spironoo/miro-cases/Images/3 Miros.jpg

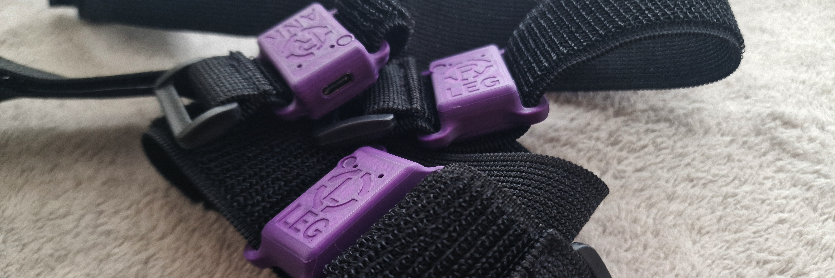
Images/3 Miros.jpg
