spironoo/miro-cases/Images/20251211_063059.jpg

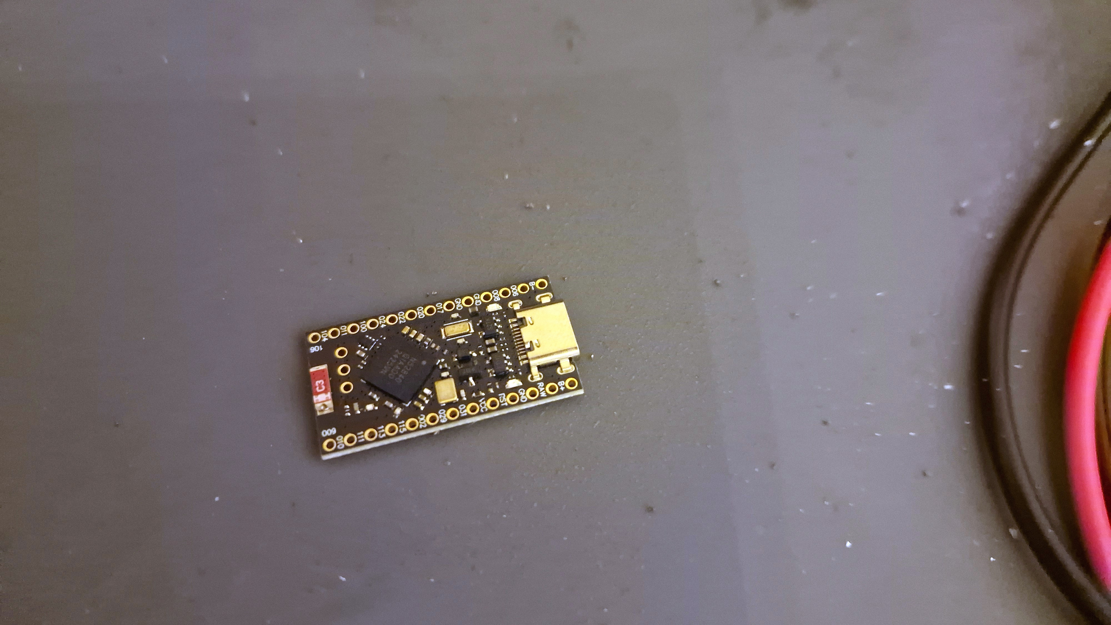
Images/20251211_063059.jpg
