spironoo/miro-cases/Images/20251211_063324.jpg

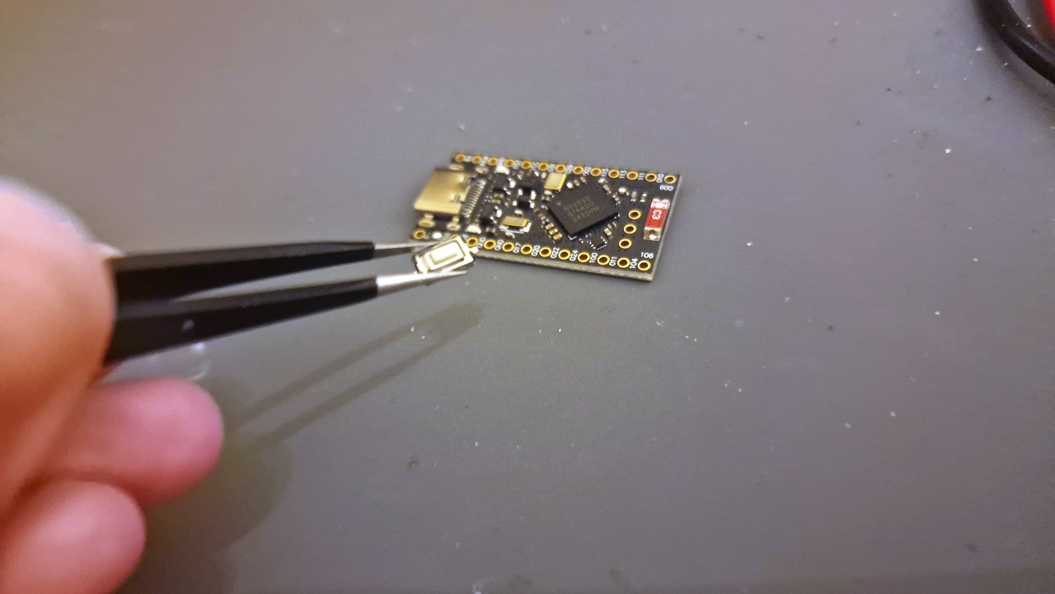
Images/20251211_063324.jpg
