spironoo/miro-cases/Images/20251211_063325.jpg

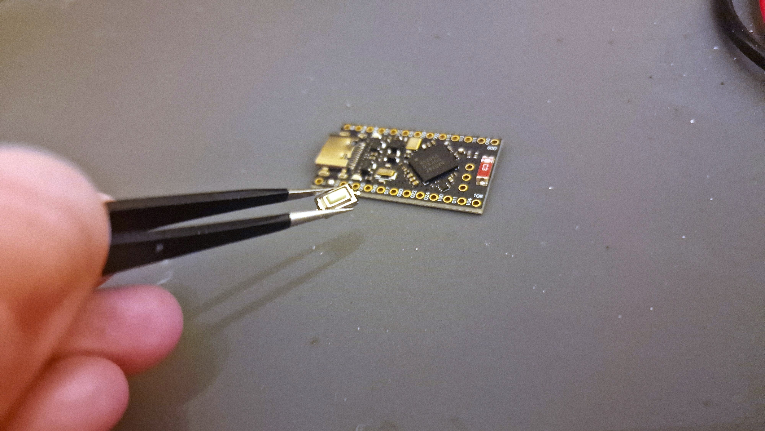
Images/20251211_063325.jpg
