spironoo/miro-cases/Images/20251211_063358.jpg

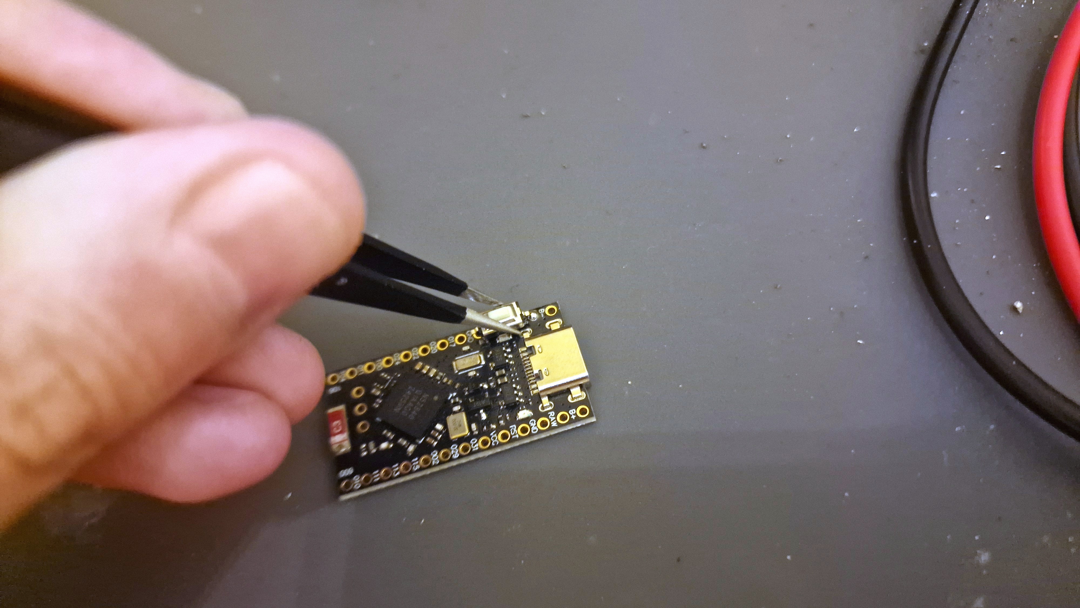
Images/20251211_063358.jpg
