spironoo/miro-cases/Images/20251211_063400.jpg

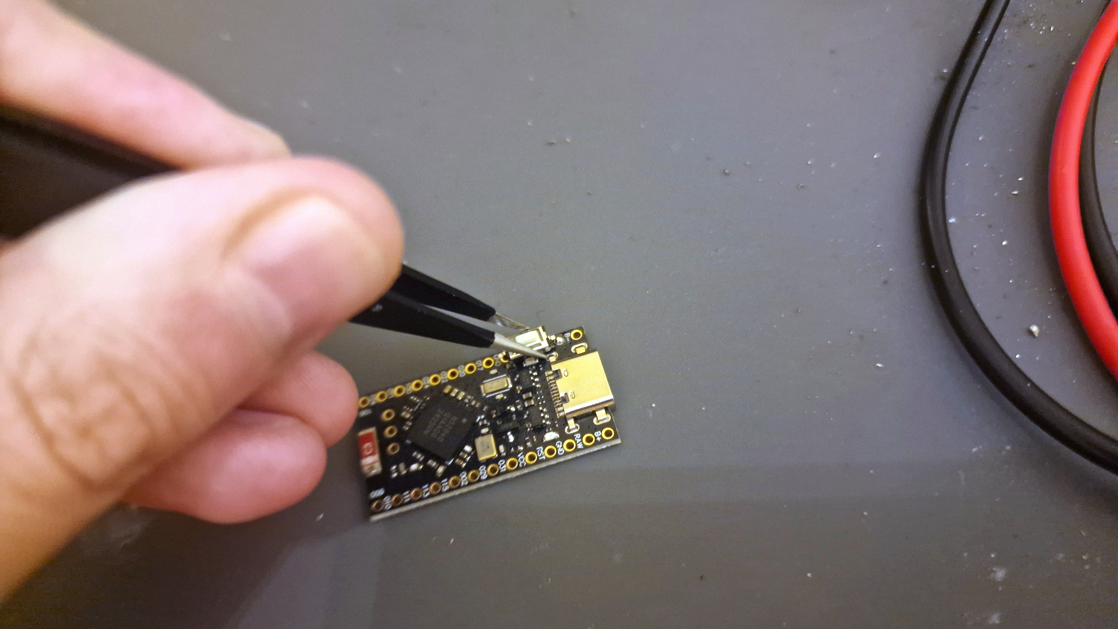
Images/20251211_063400.jpg
