spironoo/miro-cases/Images/20251211_063406.jpg

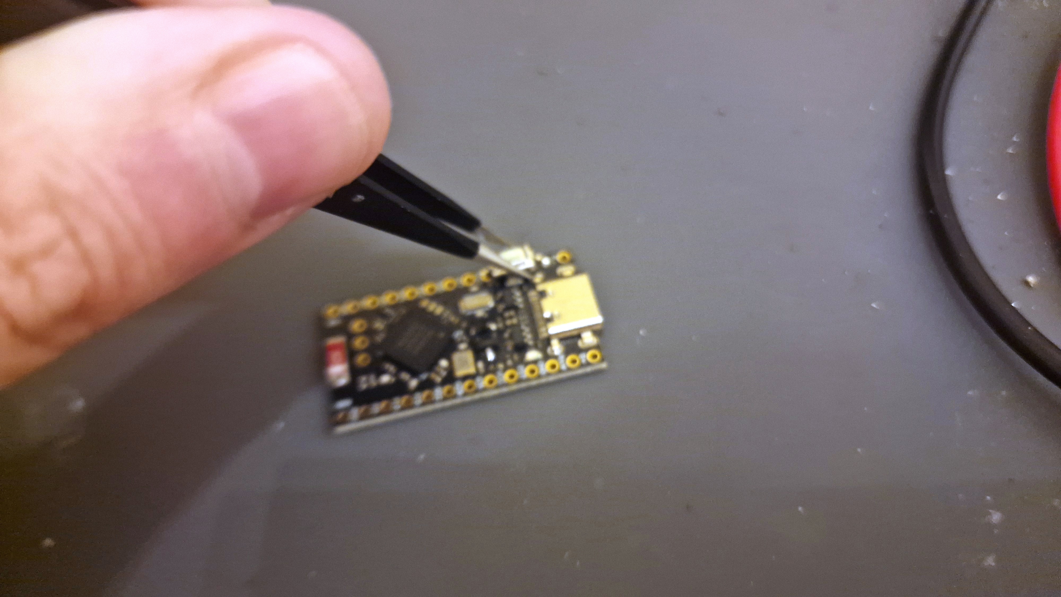
Images/20251211_063406.jpg
