spironoo/miro-cases/Images/20251211_063424.jpg

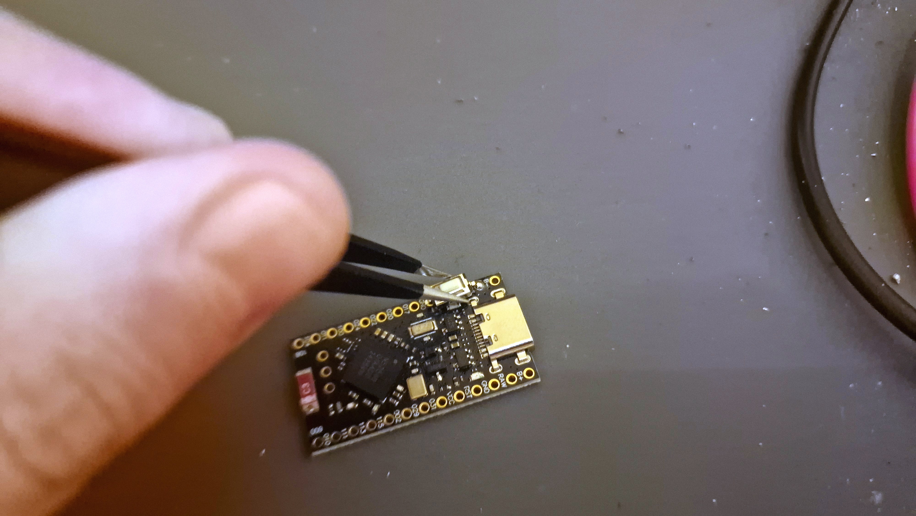
Images/20251211_063424.jpg
