spironoo/miro-cases/Images/20251211_063507.jpg

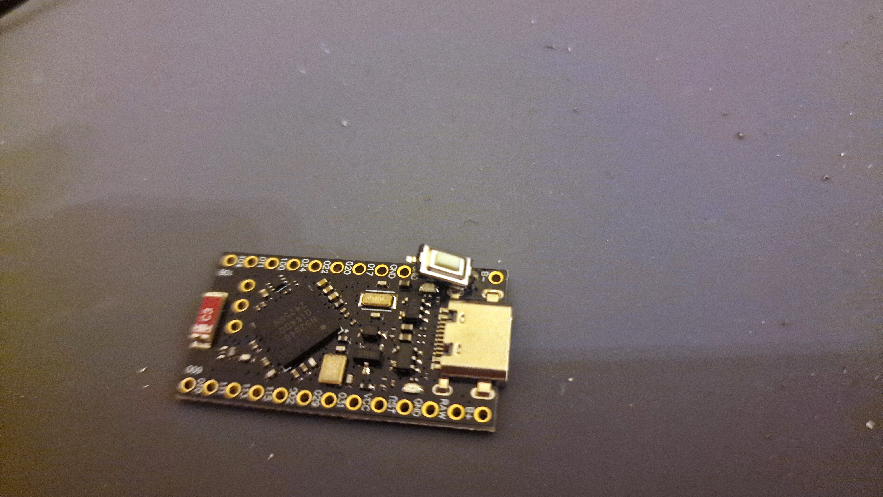
Images/20251211_063507.jpg
