spironoo/miro-cases/Images/20251211_063535.jpg

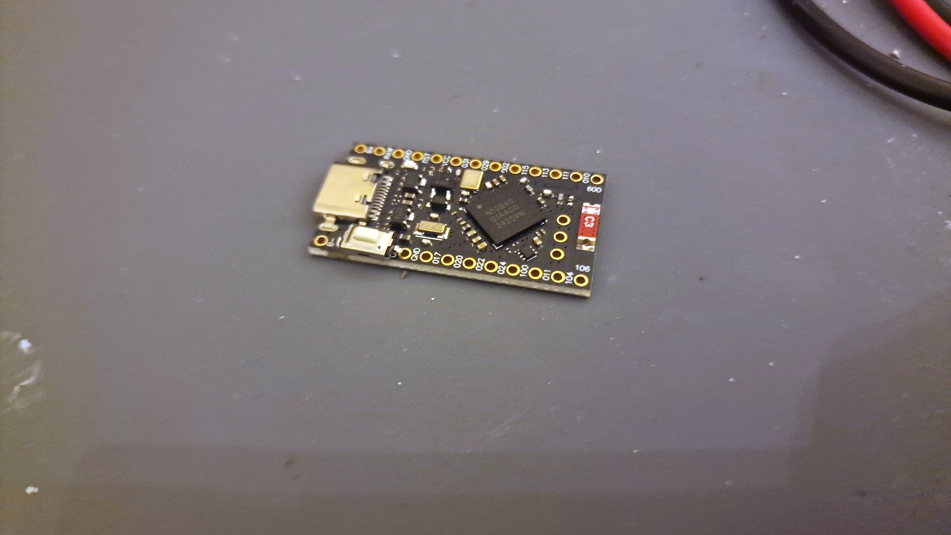
Images/20251211_063535.jpg
