spironoo/miro-cases/Images/20251211_063546.jpg

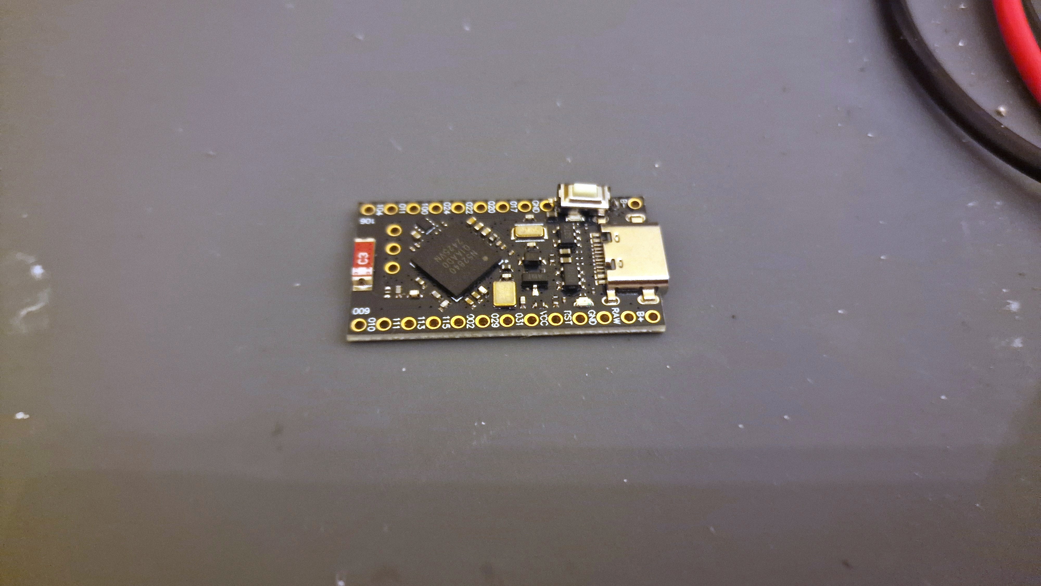
Images/20251211_063546.jpg
