spironoo/miro-cases/Images/20251211_063958.jpg

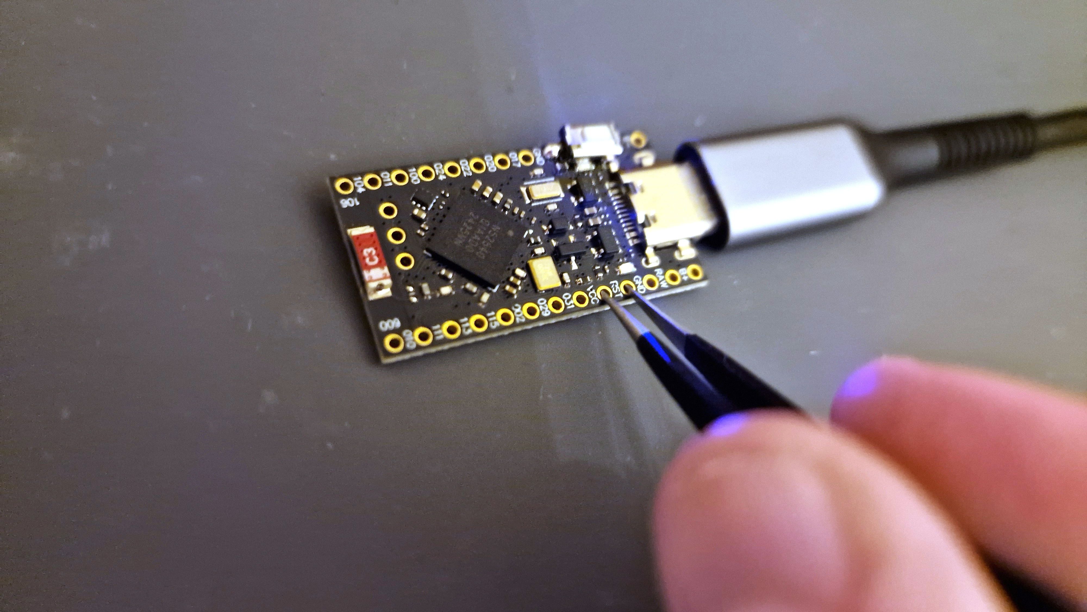
Images/20251211_063958.jpg
