spironoo/miro-cases/Images/20251211_064003.jpg

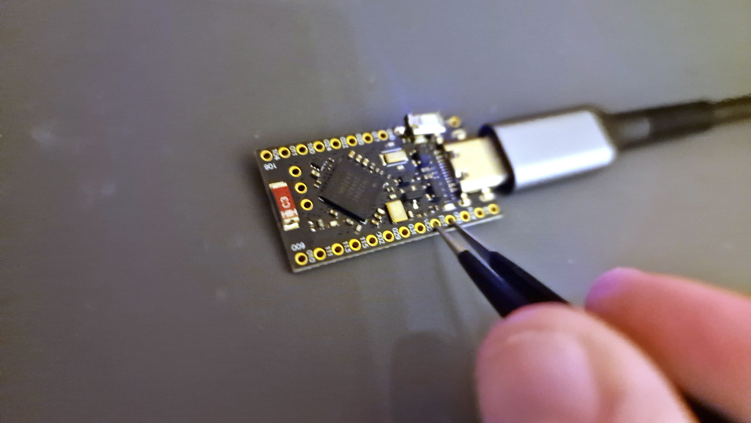
Images/20251211_064003.jpg
