spironoo/miro-cases/Images/20251211_064025.jpg

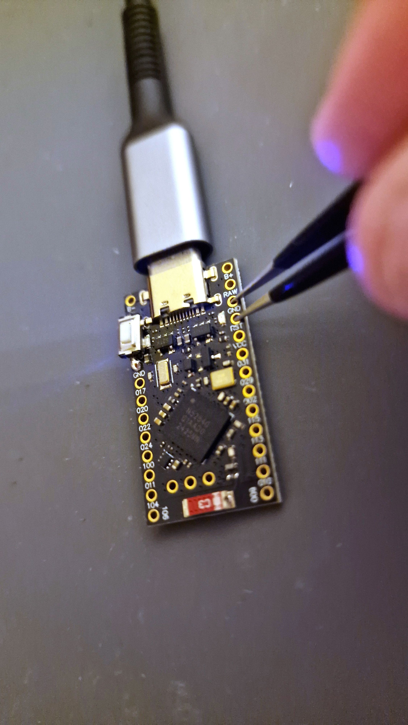
Images/20251211_064025.jpg
