spironoo/miro-cases/Images/20251211_065441.jpg

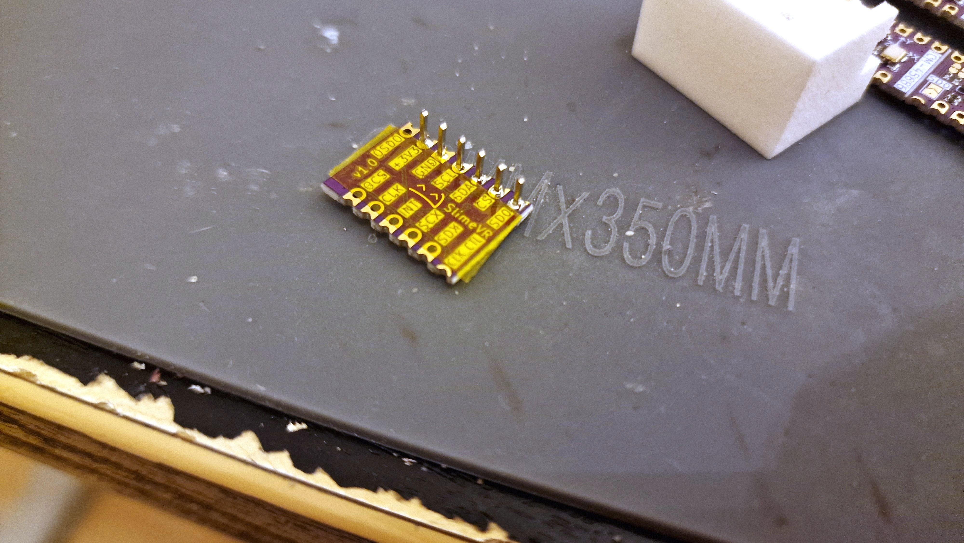
Images/20251211_065441.jpg
