spironoo/miro-cases/Images/20251211_070914.jpg

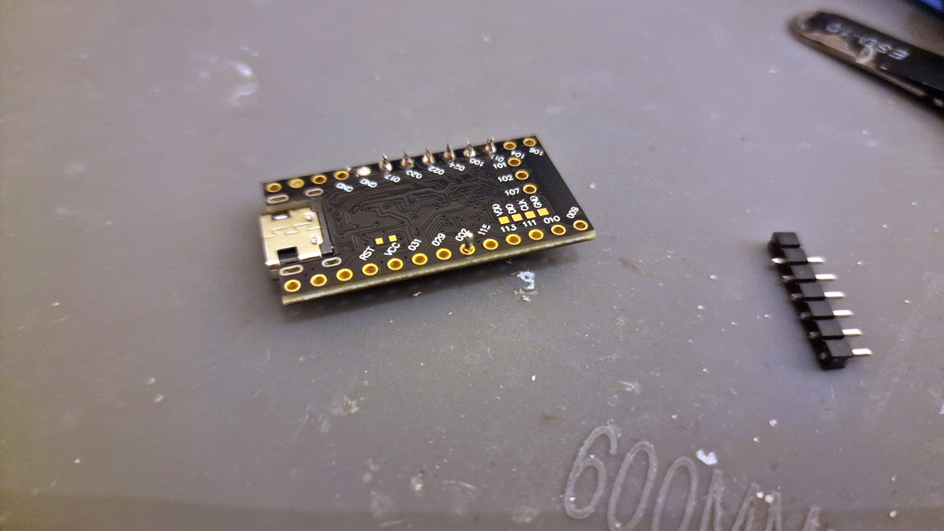
Images/20251211_070914.jpg
