spironoo/miro-cases/Images/20251211_070938.jpg

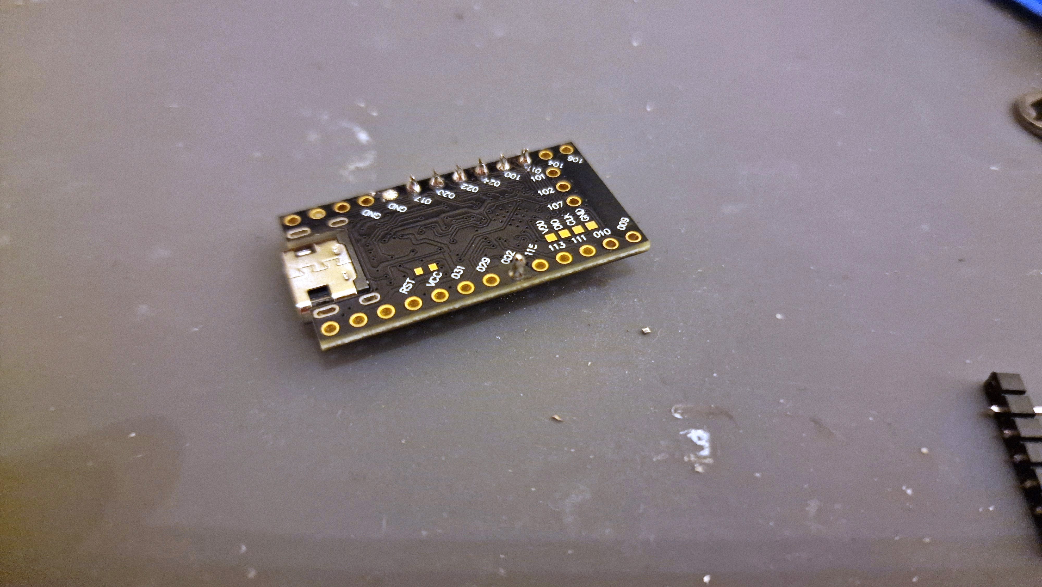
Images/20251211_070938.jpg
