spironoo/miro-cases/Images/20251211_073921.jpg

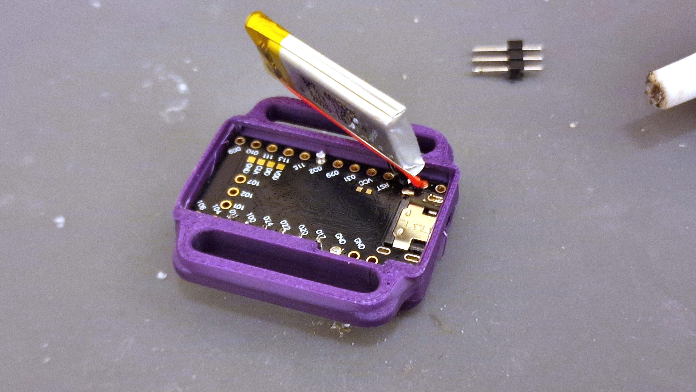
Images/20251211_073921.jpg
